smartboxchannel/EFEKTA_WIRELESS_TOUCH_SWITCH/ARDUINO SKETCH/1.png

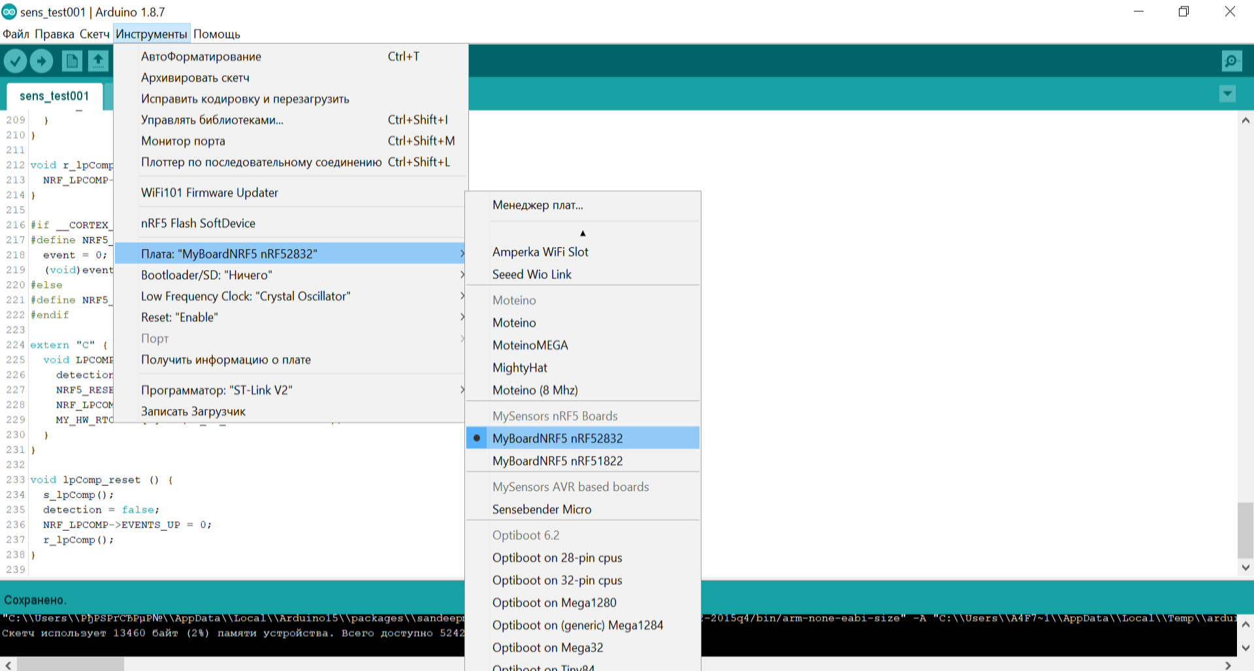
ARDUINO SKETCH/1.png
