smartboxchannel/EFEKTA_WIRELESS_TOUCH_SWITCH/GERBER_FILES/PROD/22.png

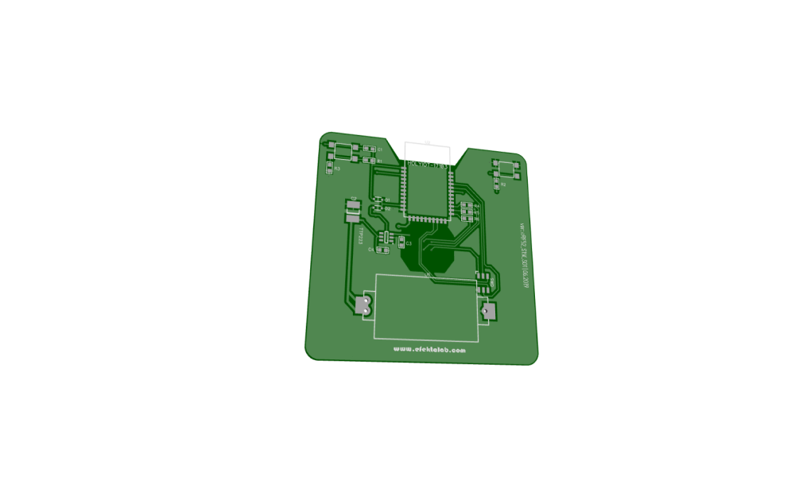
GERBER_FILES/PROD/22.png
