smartboxchannel/EFEKTA_WIRELESS_TOUCH_SWITCH/GERBER_FILES/PROD/33.png

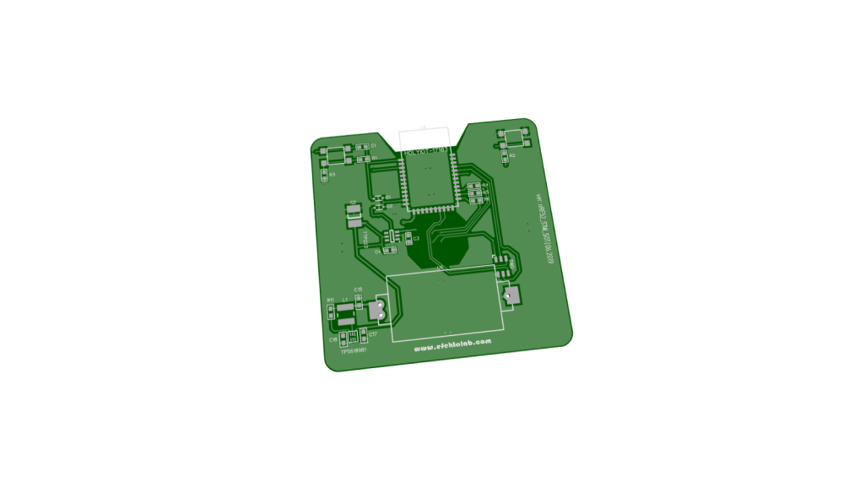
GERBER_FILES/PROD/33.png
