smartboxchannel/EFEKTA_WIRELESS_TOUCH_SWITCH/IMAGES/IMG_20190620_111730.jpg

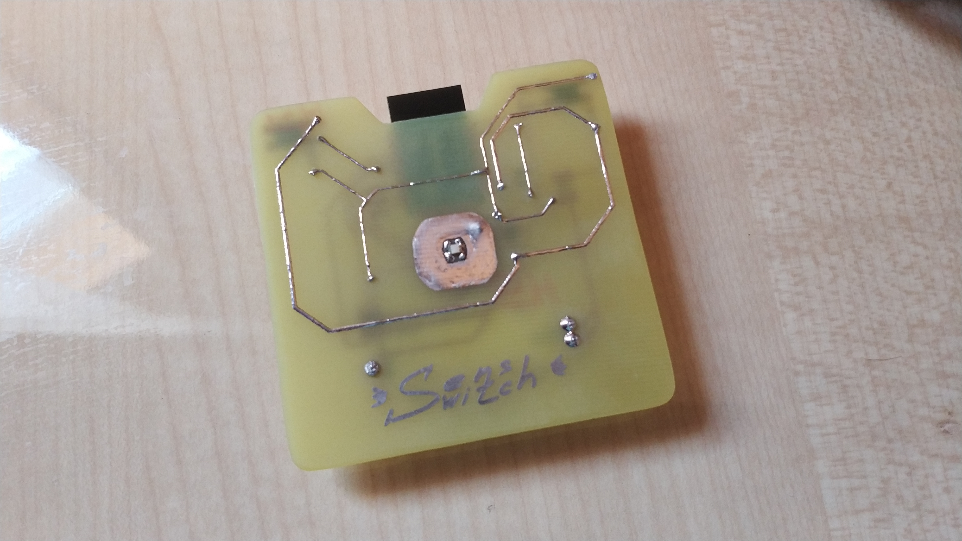
IMAGES/IMG_20190620_111730.jpg
