smartboxchannel/EFEKTA_WIRELESS_TOUCH_SWITCH/IMAGES/IMG_20190620_111739.jpg

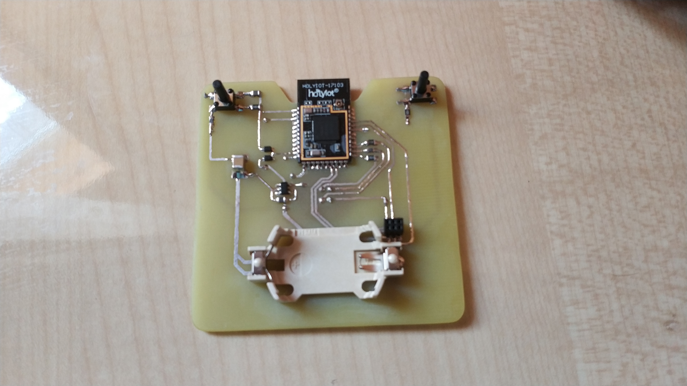
IMAGES/IMG_20190620_111739.jpg
