smartboxchannel/EFEKTA_WIRELESS_TOUCH_SWITCH/IMAGES/IMG_20190622_140526.jpg

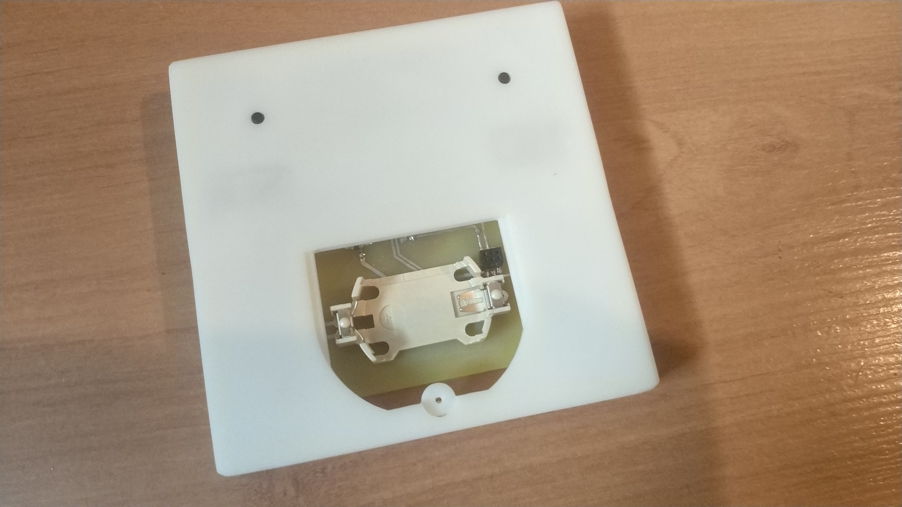
IMAGES/IMG_20190622_140526.jpg
