smartboxchannel/EFEKTA_WIRELESS_TOUCH_SWITCH/IMAGES/IMG_20190624_170039.jpg

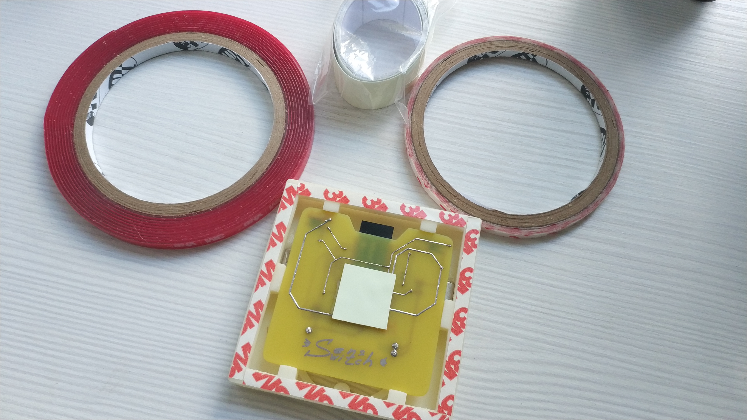
IMAGES/IMG_20190624_170039.jpg
