smartboxchannel/EFEKTA_WIRELESS_TOUCH_SWITCH/IMAGES/IMG_20190624_171030.jpg

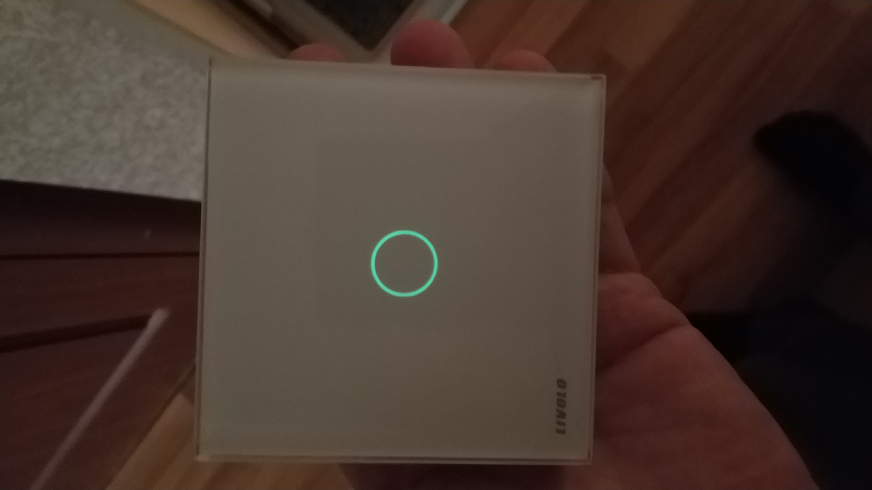
IMAGES/IMG_20190624_171030.jpg
