smartboxchannel/EFEKTA_WIRELESS_TOUCH_SWITCH/IMAGES/IMG_20190627_012020.jpg

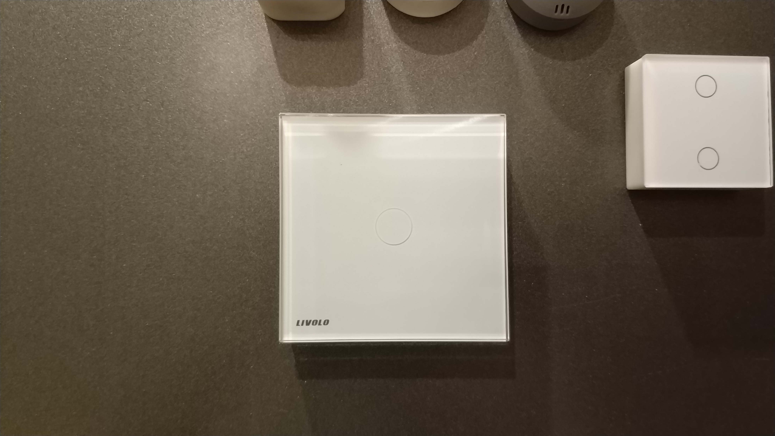
IMAGES/IMG_20190627_012020.jpg
