smartboxchannel/EFEKTA_WIRELESS_TOUCH_SWITCH/IMAGES/IMG_20190627_012106.jpg

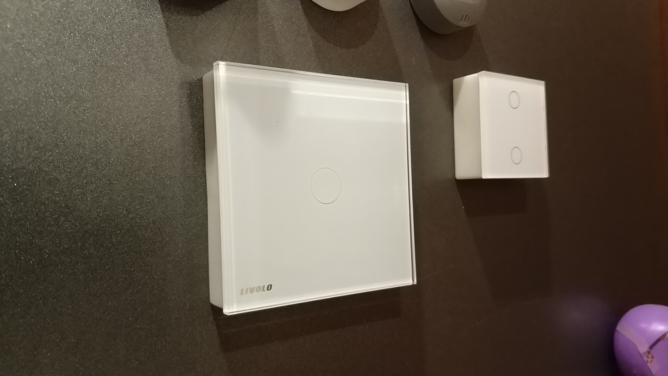
IMAGES/IMG_20190627_012106.jpg
