smartboxchannel/EFEKTA_WIRELESS_TOUCH_SWITCH/MAJORDOMO_CONTROLER/IMG_20190627_011809.jpg

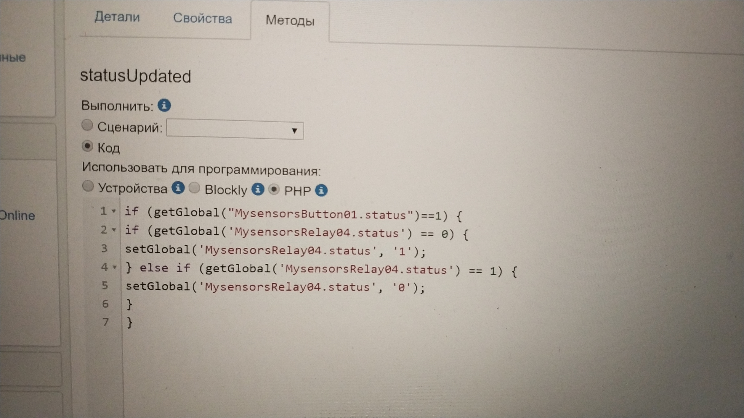
MAJORDOMO_CONTROLER/IMG_20190627_011809.jpg
